RaoneGSC/rupert/scripts/Autogen.py

import openai
import os

client = openai.OpenAI(api_key=os.environ.get("OPENAI_API_KEY"))

response = client.chat.completions.create(
    model="gpt-3.5-turbo",
    messages=[
        {"role": "system", "content": "Você é um assistente útil."},
        {"role": "user", "content": "Explique o que é machine learning."}
    ]
)

print(response.choices[0].message.content)
